DeqingSun/CH552-Automatic-Test-Jig/python/sketchTestCode/ch559_jig_code.py

import time
import serial
import serial.tools.list_ports

class CH559_jig:
    def __init__(self):
        self.PIN_CH552_P30_X =       0
        self.PIN_CH552_P31_X =       1
        self.PIN_CH552_RST_X =       2
        self.PIN_CH552_P17_X =       3
        self.PIN_CH552_P16_X =       4
        self.PIN_CH552_P15_X =       5
        self.PIN_CH552_DP_PULLUP_X = 6
        self.PIN_CH552_P34_X =       7
        self.PIN_CH552_P33_X =       8
        self.PIN_CH552_P11_X =       9
        self.PIN_EXT_LED_10_X =     10
        self.PIN_EXT_LED_11_X =     11
        self.PIN_CH552_P14_X =      12
        self.PIN_CH552_P32_X =      13
        self.PIN_CH552_P37_X =      14
        self.PIN_CH552_P36_X =      15

        self.PIN_CH559_P32 =         0
        self.PIN_CH559_P03 =         1
        self.PIN_CH559_P02 =         2
        self.PIN_CH559_P12_RC =      3
        self.PIN_CH559_P25 =         4
        self.PIN_CH559_P26 =         5
        self.PIN_CH559_P27 =         6
        self.PIN_EXT_PIN_Y7  =       7

        self.serial_port = None
        self.serial_buffer = ""
        self.uart0_buffer = ""
        self.print_serial_input = False
        

    def connect(self):
        ch559_port = None
        for port in serial.tools.list_ports.comports():
            if ((port.serial_number == "CH559 jig") or (port.serial_number == "CH559_JIG")):
                ch559_port = port
                break
        if (ch559_port == None):
            print("CH559 jig not found")
            return False
        try:
            self.serial_port = serial.Serial(ch559_port.device, 115200, timeout=0)
        except Exception as e:
            print("CH559 jig open failed on "+ch559_port.device+" with error: "+type(e).__name__)
            return False
        if (self.serial_port == None):
            print("CH559 jig open failed on "+ch559_port.device)
            return False
        return True
        
    def disconnect(self):
        if (self.serial_port == None):
            return
        self.serial_port.close()
        self.serial_port = None

    def check_input(self):
        return_list = []
        if (self.serial_port == None):
            return return_list
        if (self.serial_port.in_waiting == 0):
            return return_list
        input_bytes = self.serial_port.read(self.serial_port.in_waiting)
        input_string = input_bytes.decode('ascii', errors='ignore')
        while ( (pos_newline := input_string.find('\n')) >=0 ):
            part_before_newline = input_string[0:pos_newline]
            part_after_newline = input_string[pos_newline+1:]
            self.serial_buffer = self.serial_buffer+part_before_newline
            if (len(self.serial_buffer)>0):
                if (self.print_serial_input):
                    print(self.serial_buffer)
                if (self.serial_buffer.startswith("U:")):
                    self.uart0_buffer = self.uart0_buffer + self.serial_buffer[2:].strip("\n\r")
                return_list.append(self.serial_buffer.strip())
            self.serial_buffer = ""
            input_string = part_after_newline
        self.serial_buffer = self.serial_buffer+input_string
        return return_list
    
    def write_string_wait_for_response(self, string, string_to_wait,wait_for_input_time):
        if (self.serial_port == None):
            return ""
        if (len(string)>0):
            self.serial_port.write(string.encode('ascii'))
        if (wait_for_input_time == 0):
            #assume the command got processed successfully
            return ""
        else:
            #wait for the input
            if (len(string)>0):
                self.serial_port.flush()
            start_time = time.monotonic()
            while (time.monotonic() - start_time < wait_for_input_time):
                time.sleep(0.001)
                response = self.check_input()
                if (len(response) > 0):
                    for line in response:
                        if string_to_wait in line:
                            return line
            return ""
    
    def initailize(self, wait_for_input_time=0):
        command = "I\n"
        write_response = self.write_string_wait_for_response(command, "I:", wait_for_input_time)
        if (wait_for_input_time == 0):
            return True
        else:
            return (len(write_response)>0)

    def connect_pins(self, pin_CH552, pin_CH559, wait_for_input_time=0):
        command = f"C{pin_CH552:X}{pin_CH559:X}\n"
        write_response = self.write_string_wait_for_response(command, "C:", wait_for_input_time)
        if (wait_for_input_time == 0):
            return True
        else:
            return (len(write_response)>0)
        
    def disconnect_pins(self, pin_CH552, pin_CH559, wait_for_input_time=0):
        command = f"c{pin_CH552:X}{pin_CH559:X}\n"
        write_response = self.write_string_wait_for_response(command, "c:", wait_for_input_time)
        if (wait_for_input_time == 0):
            return True
        else:
            return (len(write_response)>0)
        
    def digital_pin_subscribe(self, pin, wait_for_input_time=0):
        command = f"r{pin:02d}\n"
        responseHeader = f"r{pin:02d}:"
        write_response = self.write_string_wait_for_response(command, responseHeader, wait_for_input_time)
        if (wait_for_input_time == 0):
            return None
        else:
            if (len(write_response)>0):
                try:
                    colon_pos = write_response.find(":")
                    return (int(write_response[colon_pos+1])>0)
                except:
                    return None
            else:
                return None
            
    def analog_pin_subscribe(self, pin, wait_for_input_time=0):
        command = f"a{pin:02d}\n"
        responseHeader = f"a{pin:02d}:"
        write_response = self.write_string_wait_for_response(command, responseHeader, wait_for_input_time)
        if (wait_for_input_time == 0):
            return None
        else:
            if (len(write_response)>0):
                try:
                    colon_pos = write_response.find(":")
                    return (int(write_response[colon_pos+1:]))
                except:
                    return None
            else:
                return None
    
    def check_digital_pin_subscription(self, pin, wait_for_input_time=0):
        command = ""
        responseHeader = f"r{pin:02d}:"
        write_response = self.write_string_wait_for_response(command, responseHeader, wait_for_input_time)
        if (wait_for_input_time == 0):
            return None
        else:
            if (len(write_response)>0):
                try:
                    colon_pos = write_response.find(":")
                    return (int(write_response[colon_pos+1])>0)
                except:
                    return None
            else:
                return None
    
    def check_analog_pin_subscription(self, pin, wait_for_input_time=0):
        command = ""
        responseHeader = f"a{pin:02d}:"
        write_response = self.write_string_wait_for_response(command, responseHeader, wait_for_input_time)
        if (wait_for_input_time == 0):
            return None
        else:
            if (len(write_response)>0):
                try:
                    colon_pos = write_response.find(":")
                    return (int(write_response[colon_pos+1:]))
                except:
                    return None
            else:
                return None
    
    def analog_read(self, pin, wait_for_input_time=1):
        command = f"A{pin:02d}\n"
        responseHeader = f"A{pin:02d}:"
        write_response = self.write_string_wait_for_response(command, responseHeader, wait_for_input_time)
        if (wait_for_input_time == 0):
            return None
        else:
            if (len(write_response)>0):
                try:
                    colon_pos = write_response.find(":")
                    return (int(write_response[colon_pos+1:]))
                except:
                    return None
            else:
                return None
            
    def analog_write(self, pin, value, wait_for_input_time=0):
        command = f"w{pin:02d}{value:02x}\n"
        write_response = self.write_string_wait_for_response(command, f"w{pin:02d}:", wait_for_input_time)
        if (wait_for_input_time == 0):
            return True
        else:
            if (len(write_response)==0):
                return False
            if ("not valid" in write_response):
                return False
            return True
    
    def digital_write(self, pin, value, wait_for_input_time=0):
        if (value == True):
            value = 1
        if (value == False):
            value = 0
        command = f"W{pin:02d}{value}\n"
        write_response = self.write_string_wait_for_response(command, f"W{pin:02d}:", wait_for_input_time)
        if (wait_for_input_time == 0):
            return True
        else:
            if (len(write_response)==0):
                return False
            if ("not valid" in write_response):
                return False
            return True
        
    def digital_read(self, pin, wait_for_input_time=1):
        command = f"R{pin:02d}\n"
        responseHeader = f"R{pin:02d}:"
        write_response = self.write_string_wait_for_response(command, responseHeader, wait_for_input_time)
        if (wait_for_input_time == 0):
            return None
        else:
            if (len(write_response)>0):
                try:
                    colon_pos = write_response.find(":")
                    return (int(write_response[colon_pos+1])>0)
                except:
                    return None
            else:
                return None
            
    def enter_bootloader_mode(self):
        command = "B\n"
        write_response = self.write_string_wait_for_response(command, "B:", 1)
        if (len(write_response)==0):
            return False
        return True
    
    def reboot_target(self):
        #force wait
        command = "b\n"
        write_response = self.write_string_wait_for_response(command, "b:", 1)
        if (len(write_response)==0):
            return False
        return True
    
    def init_uart0(self, baudrate=115200, wait_for_input_time=1):
        baudrateMuliplexer = int(baudrate/9600)
        command = f"T{baudrateMuliplexer:01x}\n"
        responseHeader = f"T:"
        write_response = self.write_string_wait_for_response(command, responseHeader, wait_for_input_time)
        if (wait_for_input_time == 0):
            return None
        else:
            if (len(write_response)>0):
                try:
                    colon_pos = write_response.find(":")
                    after_pos_content = write_response[colon_pos+1:]
                    if after_pos_content == "disable UART":
                        return 0
                    else:
                        return (int(after_pos_content))
                except:
                    return None
            else:
                return None
    
    def uart0_send_string(self, string_to_send):
        string_to_send = string_to_send.replace("\n", "\\n")
        string_to_send = string_to_send.replace("\r", "\\r")
        command = f"U{string_to_send}\n"
        self.write_string_wait_for_response(command, "", 0)
        return
    
    def uart0_get_buffered_string(self, escape_characters=True):
        buffer_string = self.uart0_buffer
        self.uart0_buffer = ""
        if (escape_characters):
            buffer_string = buffer_string.replace("\\n", "\n")
            buffer_string = buffer_string.replace("\\r", "\r")
        return buffer_string
